EpicPantalones/340-board/LTSpice/transmitter/transmitter.asc

D1: LED; myled
M1: nmos; 2N7002
R1: res; 8.9
R2: res; 330
V1: voltage; 3.3
V2: voltage; 3.3
Named nets: 0
.model myled D(Is=6e-17 Rs=1.9 N=2 type=LED)
.tran 3000
