EpicPantalones/340-board/LTSpice/receiver/receiver_1A.asc

C1: cap; {CH}
C2: cap; {CL}
C3: cap; 1m
C4: cap; 1m
C5: cap; 100n
C6: cap; 100n
C7: cap; {CL}
C8: cap; {CH}
C9: cap; 1µ
In1: current; 1m; AC 1
In2: current; SINE(0 400n 60); AC 1
In3: current; SINE(0 400n 40k); AC 1
Is: current; SINE(0 40n {freq_Lsr}); AC 1
R1: res; {RH}
R2: res; {RL}
R3: res; {RL}
R4: res; {RH}
R5: res; {Rsp}
R6: res; {Rsp}
R7: res; 2k
R8: res; 100
R9: res; 100
U1: UniversalOpAmp2; Avol=25k GBW=1Meg Slew=0.6Meg; Ilimit=6m Rail=25m Vos=0
U2: UniversalOpAmp2; Avol=25k GBW=1Meg Slew=0.6Meg; Ilimit=6m Rail=25m Vos=0
Vsupply: voltage; SINE(3.3 30m 2632)
Named nets: vn, vp, out, 0
.param Rsp=1k
.tran 50ms
.step param freq_Lsr list 1471 1724 2000 2273 2941 3333 3571 3846 4167
.meas avgV avg V(out)
;meas psrc pp V(vp)
.meas pout pp V(out)
.param CL=0.05nF
.param RL=200k
.param CH=100nF
.param RH 1k
.ac dec 0.01 100k 10
.param freq_Lsr 1471
.meas ac maxgain max mag(v(out))
.meas ac low_corner find freq when mag(v(out))=maxgain/sqrt(2)
.mease ac high_corner find freq when mag(v(out))=maxgain/sqrt(2) cross=2
